analoghifi/Thel-Power-Supplies/NT-HQ-series/docs/NT-HQ-OUT.jpg

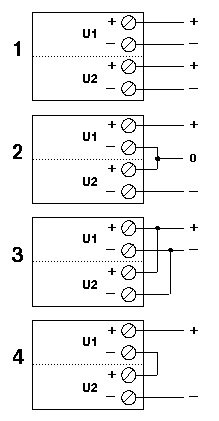
NT-HQ-series/docs/NT-HQ-OUT.jpg
