analoghifi/Thel-Power-Supplies/NT-HQ-series/docs/NTHQ.jpg

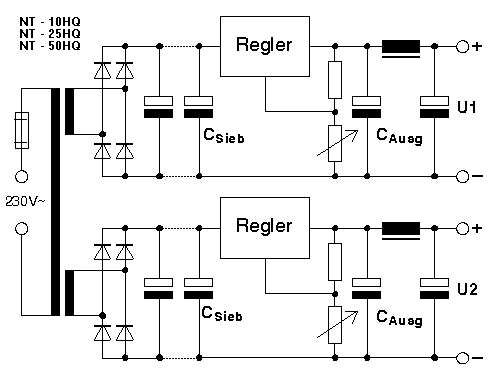
NT-HQ-series/docs/NTHQ.jpg
