analoghifi/Thel-Power-Supplies/NT-HQ-series/docs/pmax.png

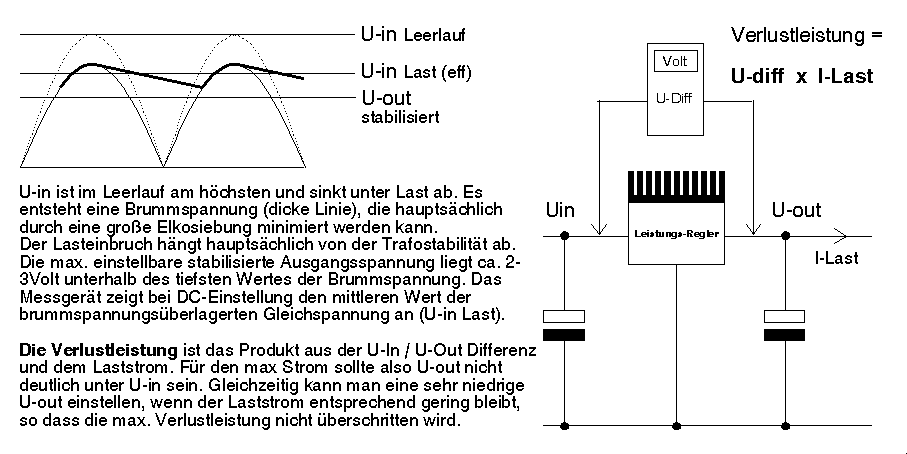
NT-HQ-series/docs/pmax.png
