analoghifi/Thel-Power-Supplies/NT-HQ-series/pics/NT-10.jpg

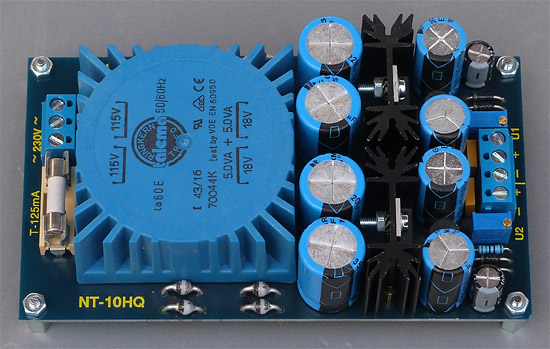
NT-HQ-series/pics/NT-10.jpg
