analoghifi/Thel-Power-Supplies/NT-HQ-series/pics/NT-25.jpg

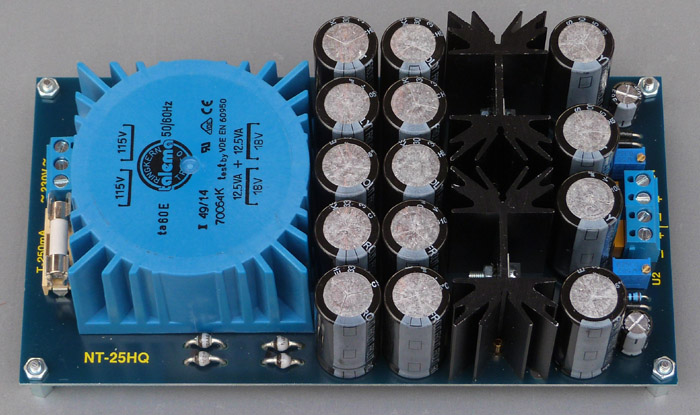
NT-HQ-series/pics/NT-25.jpg
