analoghifi/Thel-Power-Supplies/NT-HQ-series/pics/NT-50.jpg

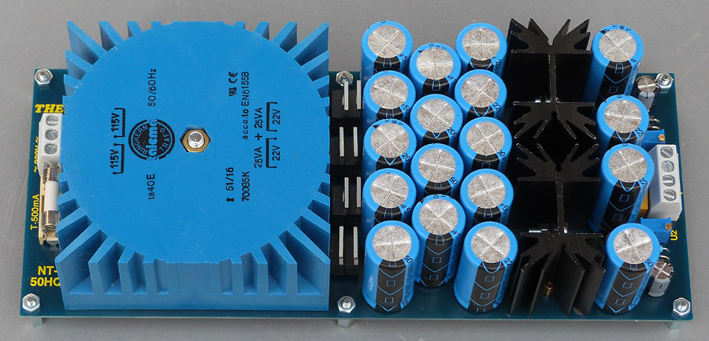
NT-HQ-series/pics/NT-50.jpg
