analoghifi/Thel-Power-Supplies/SPR5-HQ/docs/SPR-HQ.png

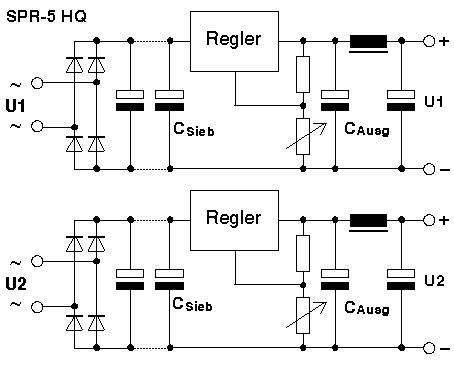
SPR5-HQ/docs/SPR-HQ.png
