analoghifi/Thel-Power-Supplies/SPR5-HQ/hardware/KiCad/original V2/PowerSupply_SPR5HQ_original_1Layer_THT_v2__3D_1.png

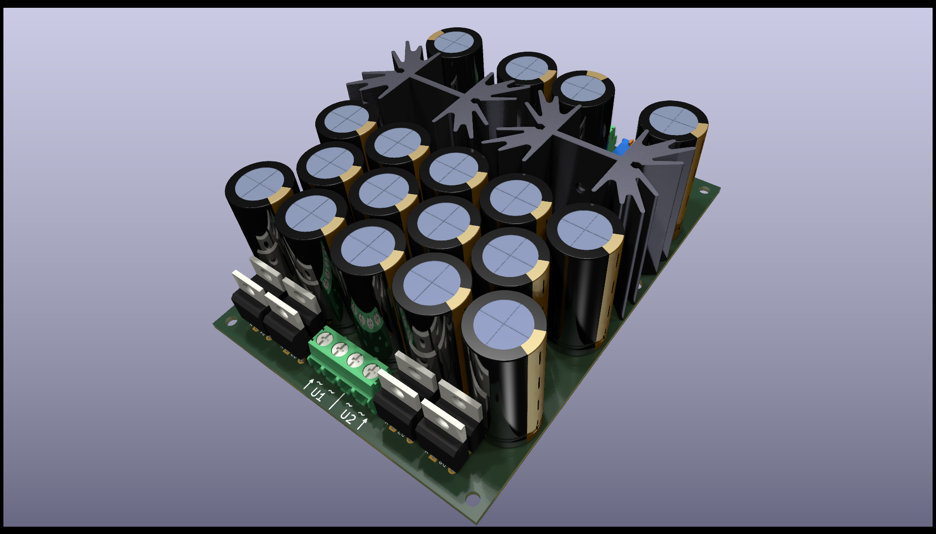
SPR5-HQ/hardware/KiCad/original V2/PowerSupply_SPR5HQ_original_1Layer_THT_v2__3D_1.png
