analoghifi/Thel-Power-Supplies/SPR5-HQ/hardware/PCB_SPR5-HQ_Bottom_shine_thru.jpg

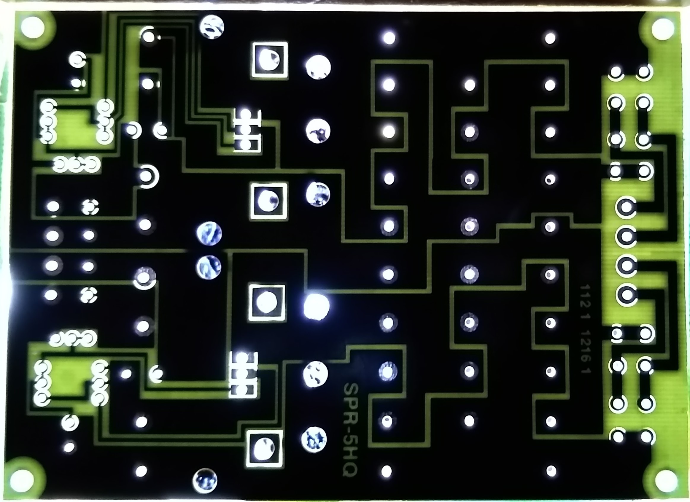
SPR5-HQ/hardware/PCB_SPR5-HQ_Bottom_shine_thru.jpg
