analoghifi/Thel-Power-Supplies/SPR5-HQ/hardware/PCB_SPR-5HQ_Bottom.jpg

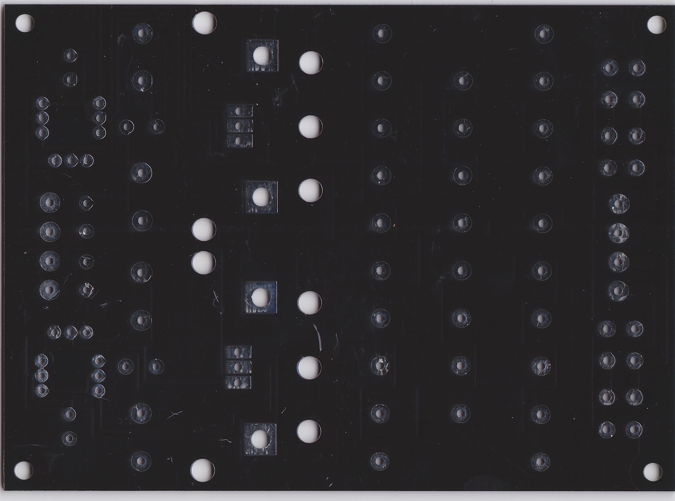
SPR5-HQ/hardware/PCB_SPR-5HQ_Bottom.jpg
